MaxTeetz/InformatikProjekt/images/enclosure.PNG

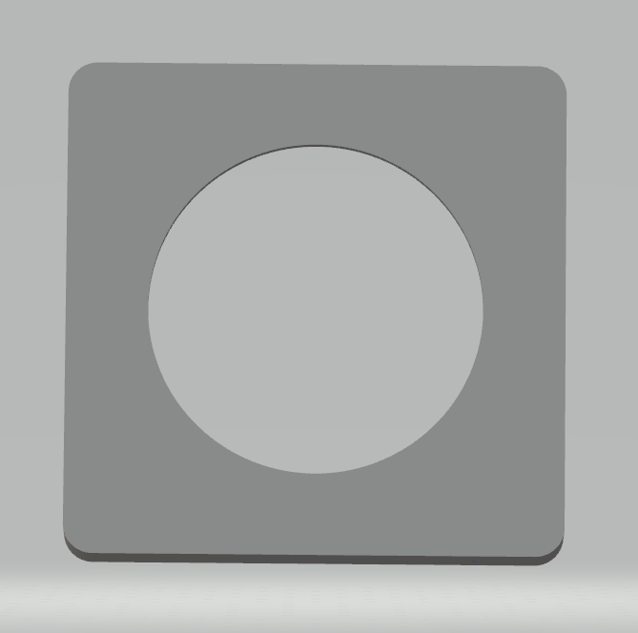
images/enclosure.PNG
