MaxTeetz/InformatikProjekt/images/knob.PNG

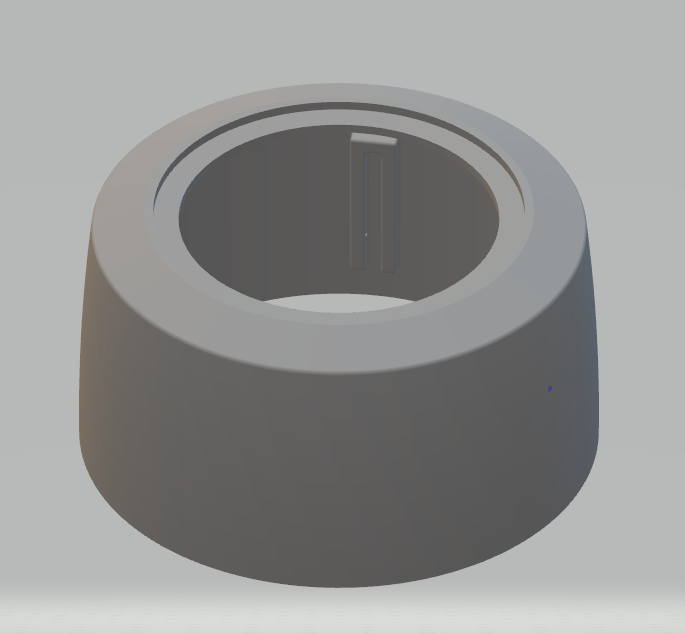
images/knob.PNG
