MaxTeetz/InformatikProjekt/images/mountbase.PNG

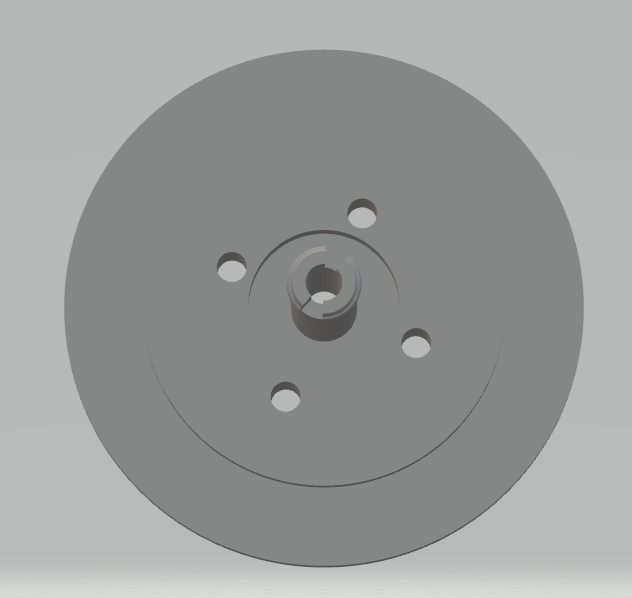
images/mountbase.PNG
